oxy-2/deltavr/obsidian files/week1 thirdspace/monizjoao/Screenshot 2026-09-20 193455.png

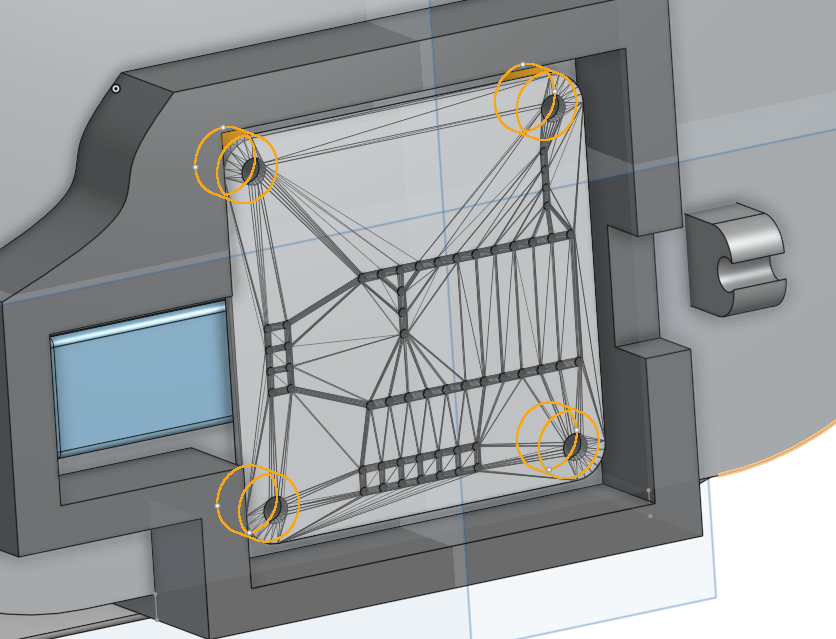
obsidian files/week1 thirdspace/monizjoao/Screenshot 2026-09-20 193455.png
