oxy-2/deltavr/obsidian files/week1 thirdspace/merekelene/emulation software showcase.png

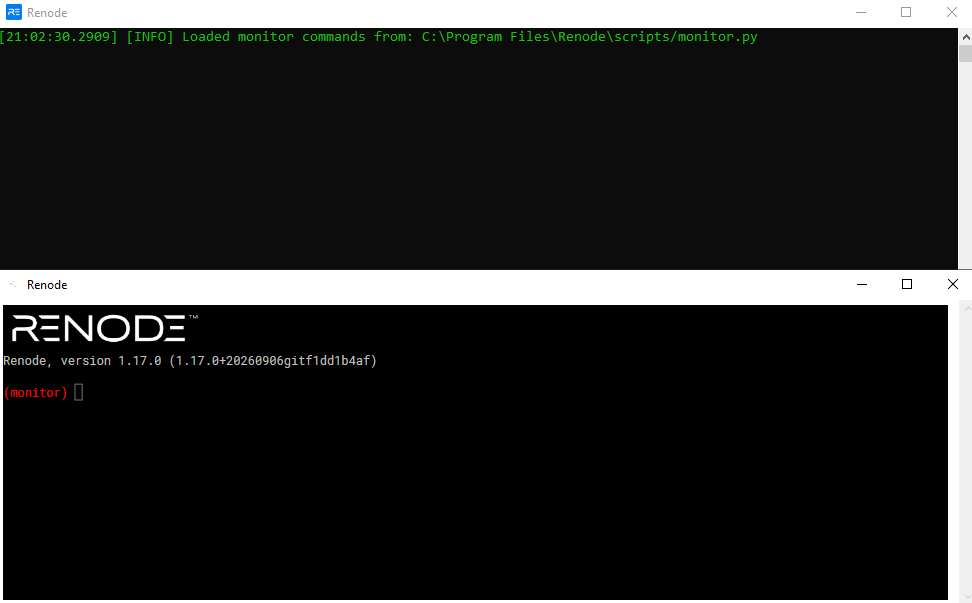
obsidian files/week1 thirdspace/merekelene/emulation software showcase.png
