oxy-2/deltavr/obsidian files/week1 thirdspace/merekelene/emulation software.png

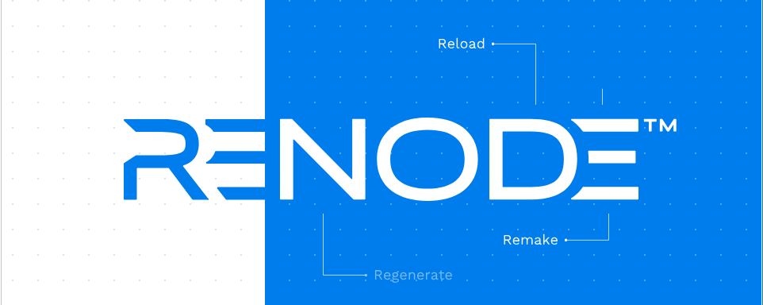
obsidian files/week1 thirdspace/merekelene/emulation software.png
