oxy-2/deltavr/obsidian files/week1 thirdspace/merekelene/pcb.png

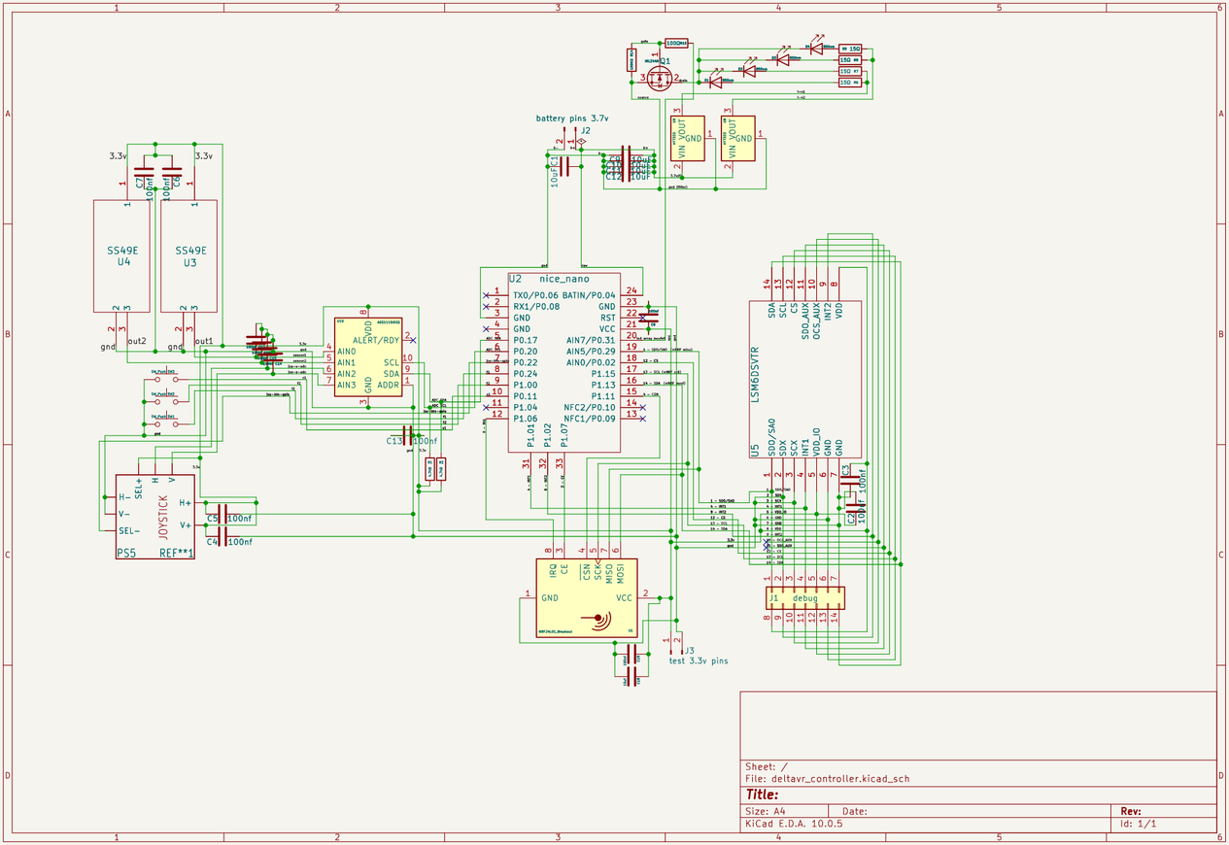
obsidian files/week1 thirdspace/merekelene/pcb.png
