oxy-2/deltavr/obsidian files/week1 thirdspace/merekelene/readable gpio pin conections.png

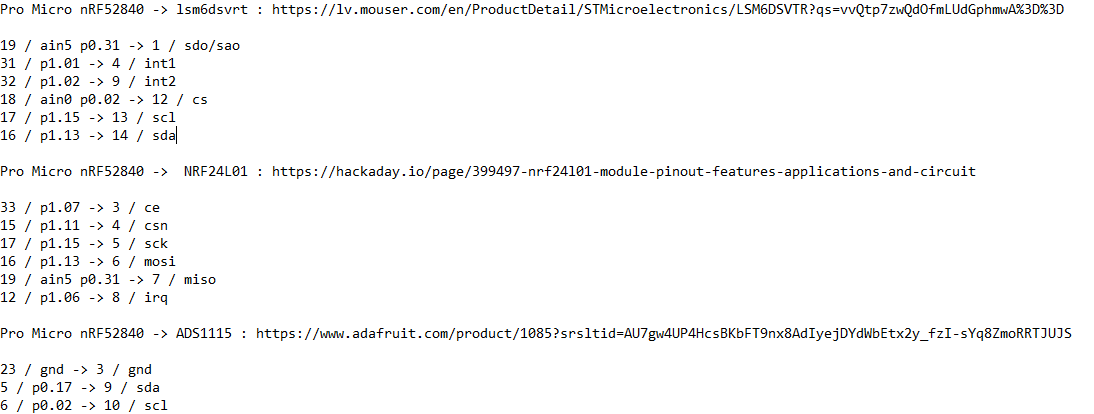
obsidian files/week1 thirdspace/merekelene/readable gpio pin conections.png
