oxy-2/deltavr/obsidian files/week1 thirdspace/monizjoao/Pasted image 20260920193406.png

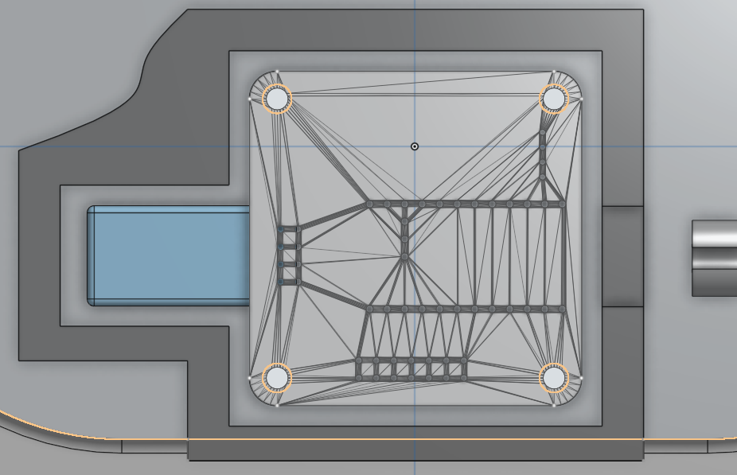
obsidian files/week1 thirdspace/monizjoao/Pasted image 20260920193406.png
