oxy-2/deltavr/obsidian files/week1 thirdspace/monizjoao/Pasted image 20260920201033.png

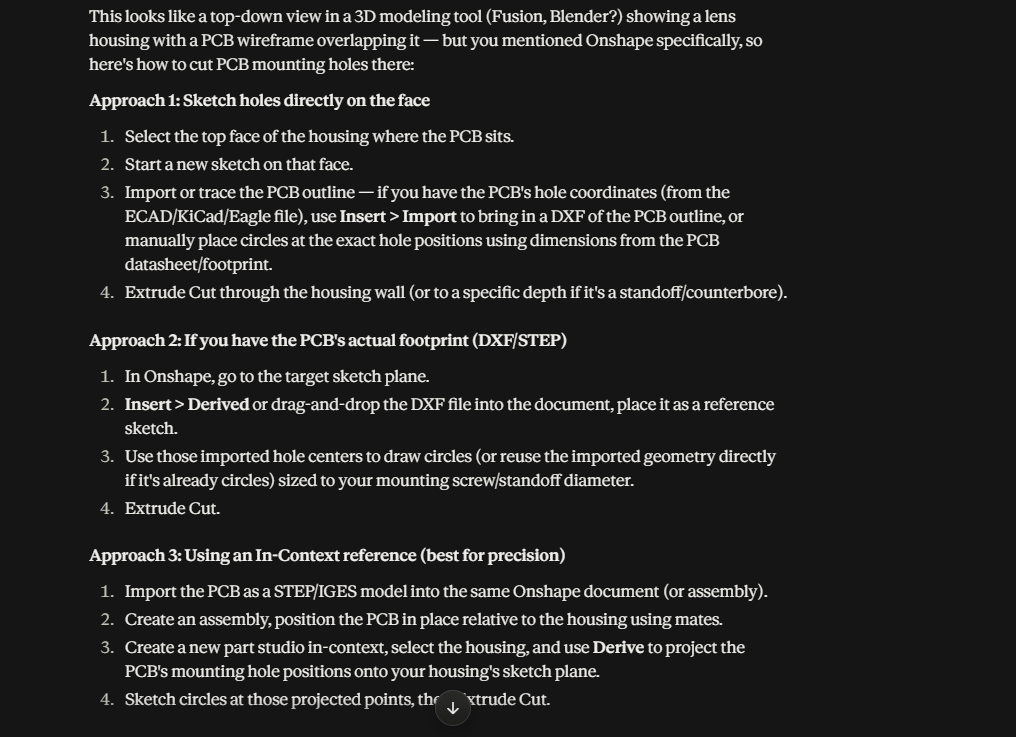
obsidian files/week1 thirdspace/monizjoao/Pasted image 20260920201033.png
