oxy-2/deltavr/obsidian files/week1 thirdspace/monizjoao/Pasted image 20260920225639.png

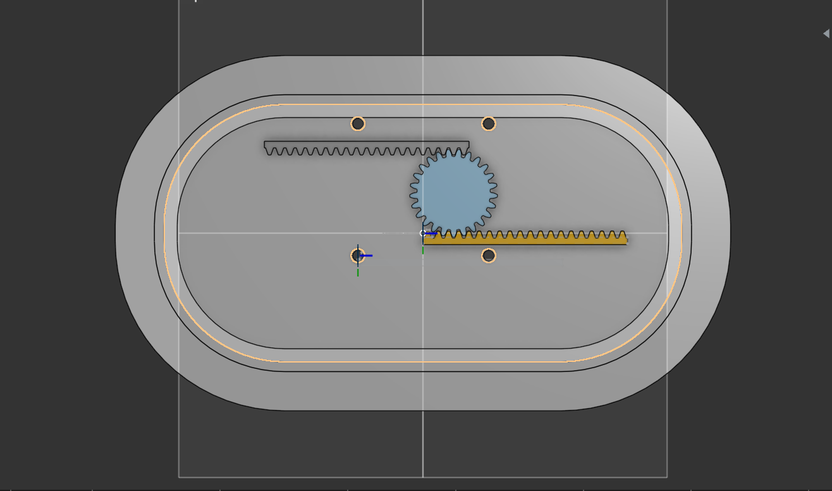
obsidian files/week1 thirdspace/monizjoao/Pasted image 20260920225639.png
