oxy-2/deltavr/obsidian files/week1 thirdspace/monizjoao/Pasted image 20260920233952.png

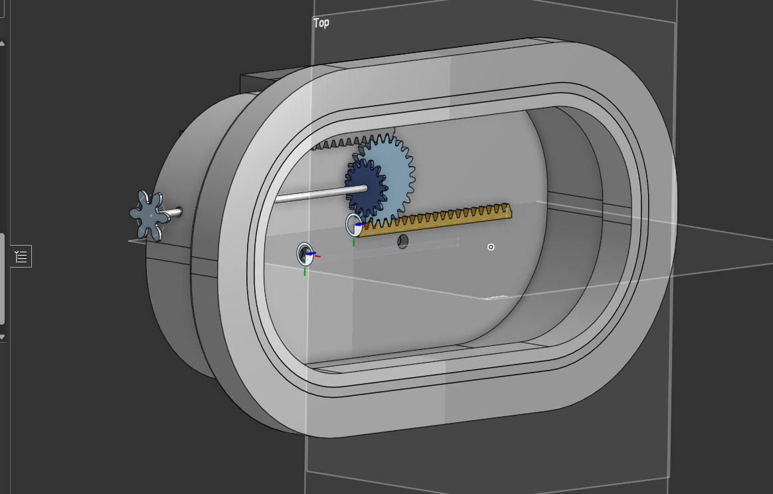
obsidian files/week1 thirdspace/monizjoao/Pasted image 20260920233952.png
