oxy-2/deltavr/obsidian files/week1 thirdspace/monizjoao/Pasted image 20260921000253.png

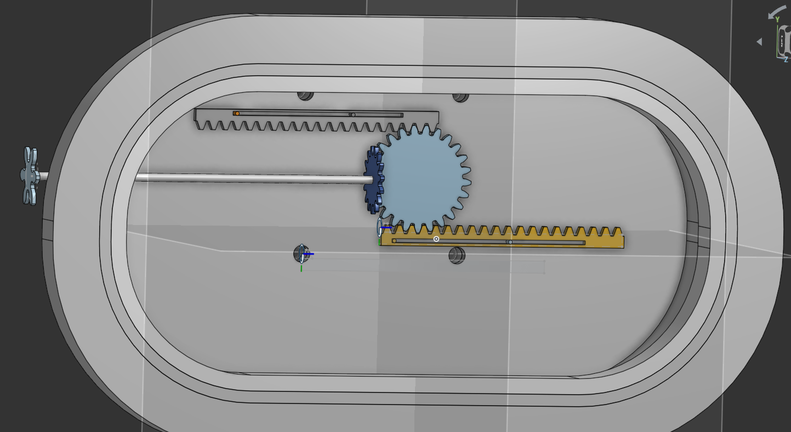
obsidian files/week1 thirdspace/monizjoao/Pasted image 20260921000253.png
