oxy-2/deltavr/obsidian files/week1 thirdspace/monizjoao/Pasted image 20260921001410.png

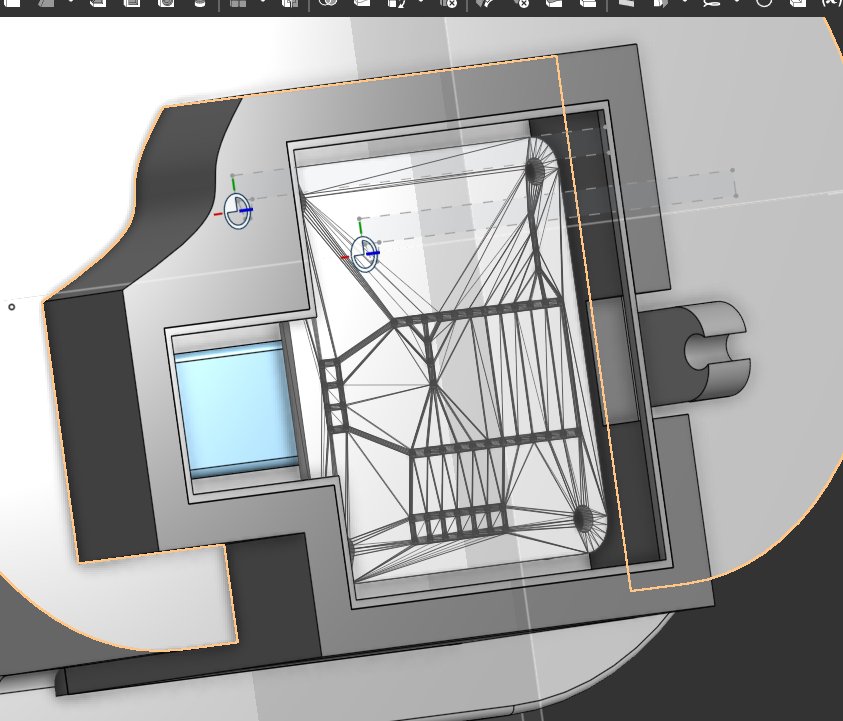
obsidian files/week1 thirdspace/monizjoao/Pasted image 20260921001410.png
