oxy-2/deltavr/obsidian files/week1 thirdspace/rhime7274/controller pcb.png

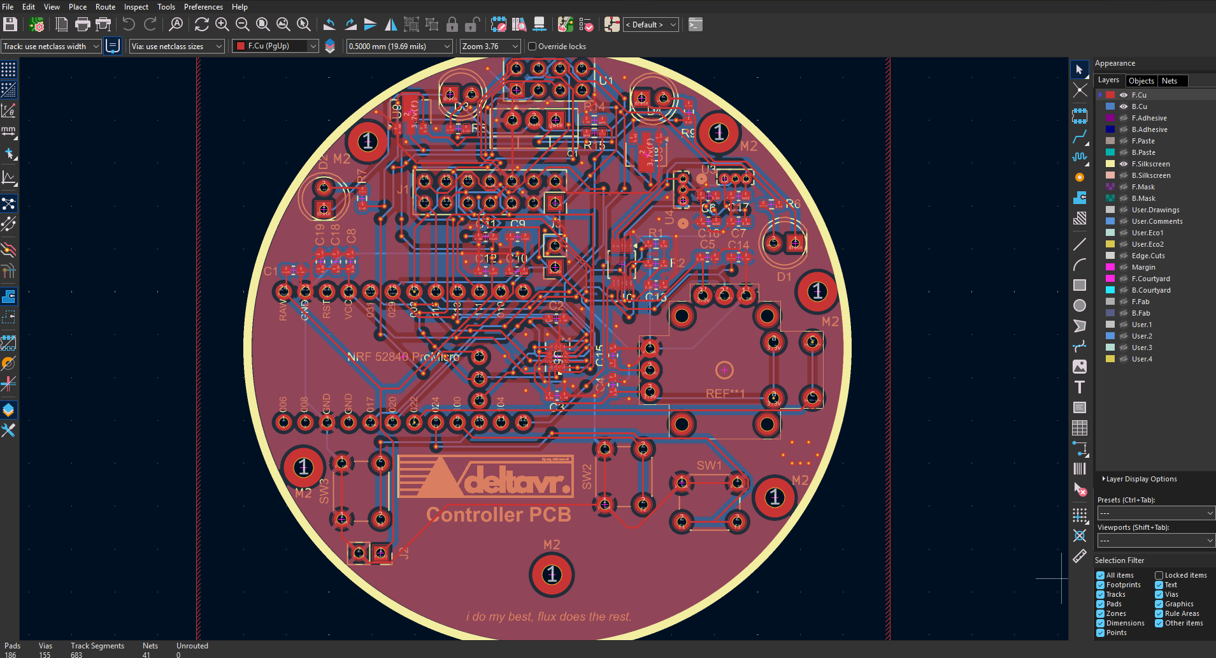
obsidian files/week1 thirdspace/rhime7274/controller pcb.png
