oxy-2/deltavr/obsidian files/week1 thirdspace/rhime7274/front page book.jpg

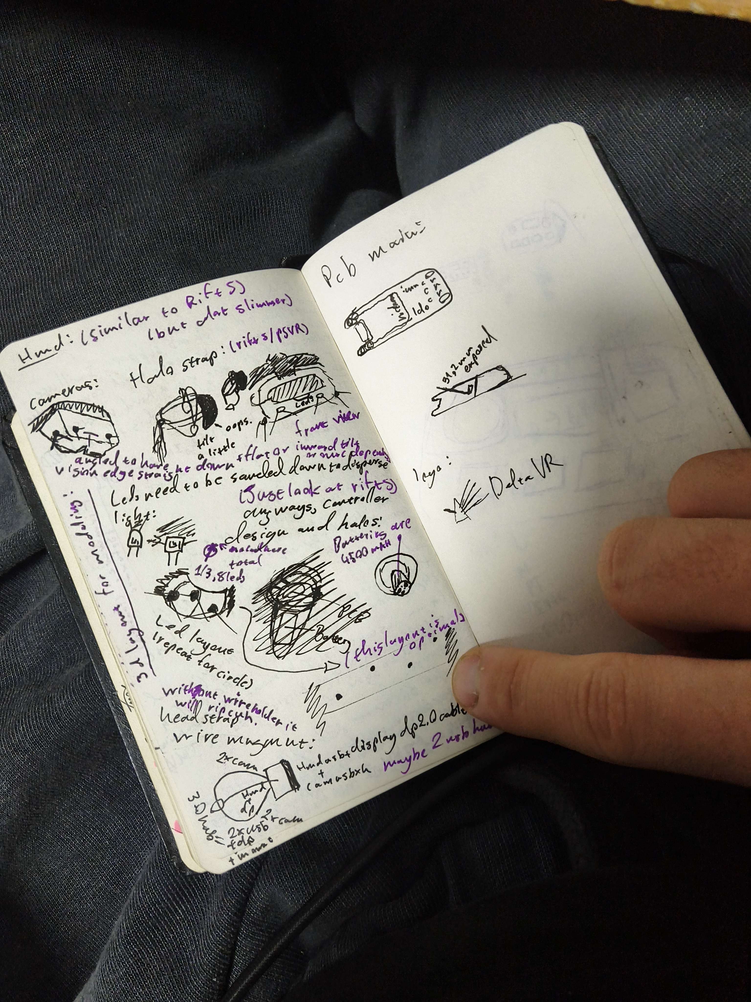
obsidian files/week1 thirdspace/rhime7274/front page book.jpg
