oxy-2/deltavr/obsidian files/week1 thirdspace/rhime7274/headset model.png

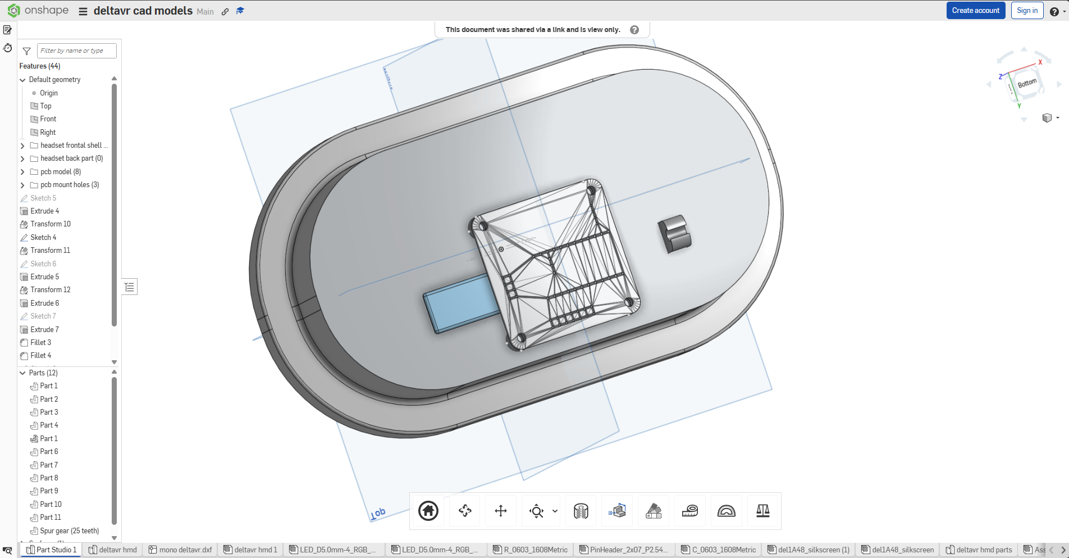
obsidian files/week1 thirdspace/rhime7274/headset model.png
