oxy-2/deltavr/obsidian files/week1 thirdspace/rhime7274/hmd pcb.jpg

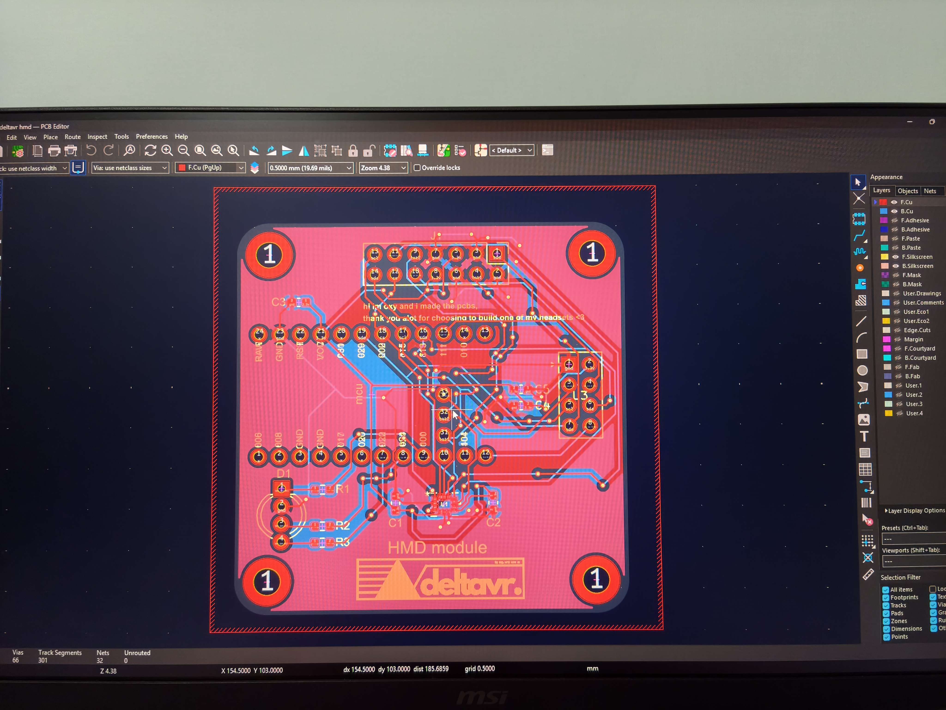
obsidian files/week1 thirdspace/rhime7274/hmd pcb.jpg
