oxy-2/deltavr/obsidian files/week2 thirdspace/merekelene/camera and lenses.png

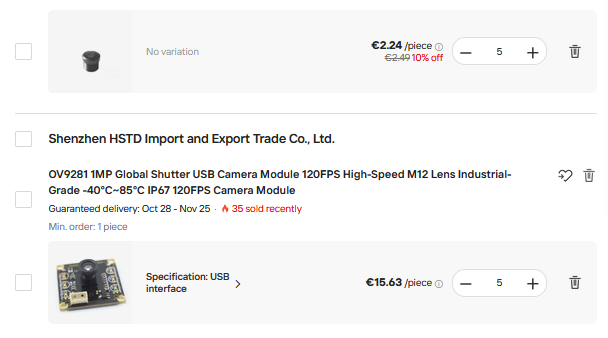
obsidian files/week2 thirdspace/merekelene/camera and lenses.png
