oxy-2/deltavr/obsidian files/week2 thirdspace/merekelene/file system showcase.png

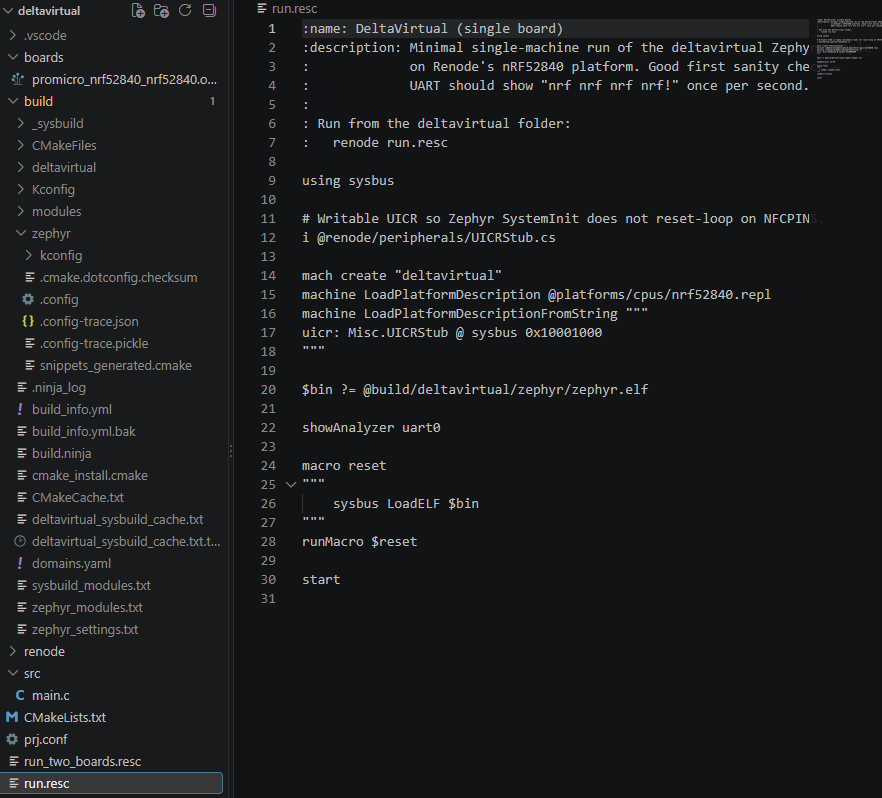
obsidian files/week2 thirdspace/merekelene/file system showcase.png
