oxy-2/deltavr/obsidian files/week2 thirdspace/merekelene/Gpio naming showcase.png

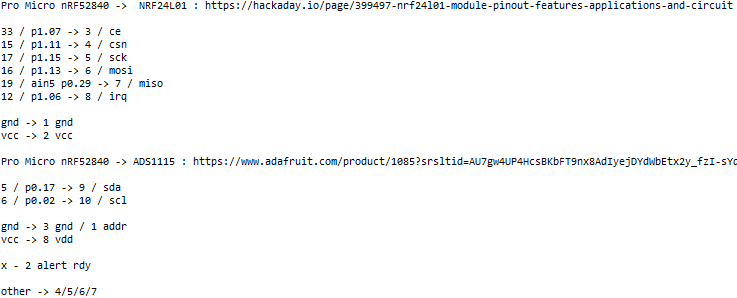
obsidian files/week2 thirdspace/merekelene/Gpio naming showcase.png
