oxy-2/deltavr/obsidian files/week2 thirdspace/merekelene/new radio module.png

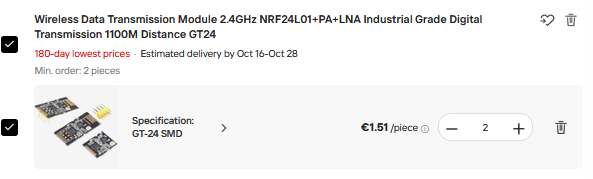
obsidian files/week2 thirdspace/merekelene/new radio module.png
