oxy-2/deltavr/obsidian files/week2 thirdspace/merekelene/uncompiled c code that will become an elf file.png

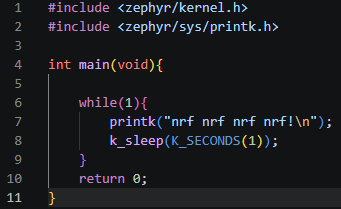
obsidian files/week2 thirdspace/merekelene/uncompiled c code that will become an elf file.png
