oxy-2/deltavr/obsidian files/week2 thirdspace/monizjoao/Pasted image 20260927151539.png

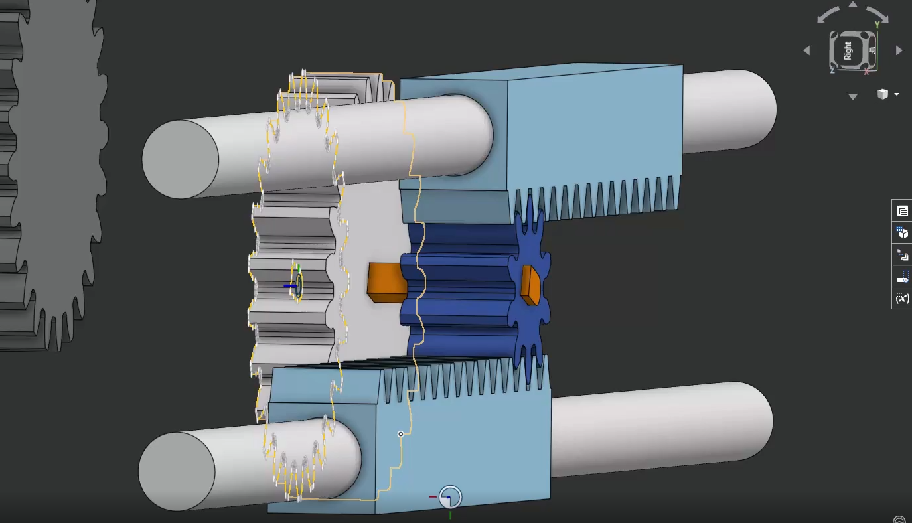
obsidian files/week2 thirdspace/monizjoao/Pasted image 20260927151539.png
