oxy-2/deltavr/obsidian files/week2 thirdspace/monizjoao/Pasted image 20260927153908.png

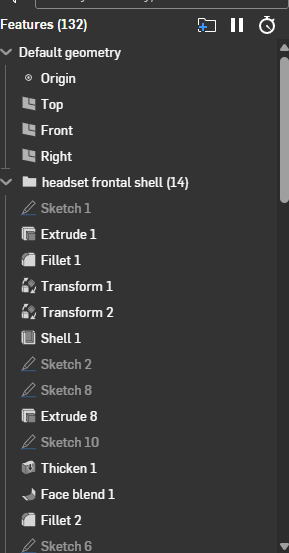
obsidian files/week2 thirdspace/monizjoao/Pasted image 20260927153908.png
