oxy-2/deltavr/obsidian files/week2 thirdspace/monizjoao/Pasted image 20260927155630.png

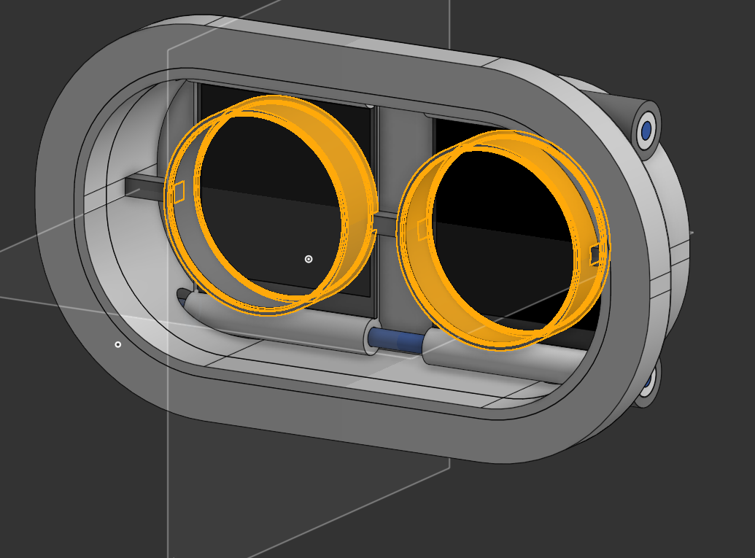
obsidian files/week2 thirdspace/monizjoao/Pasted image 20260927155630.png
