oxy-2/deltavr/obsidian files/week2 thirdspace/rhime7274/censored doc p2.png

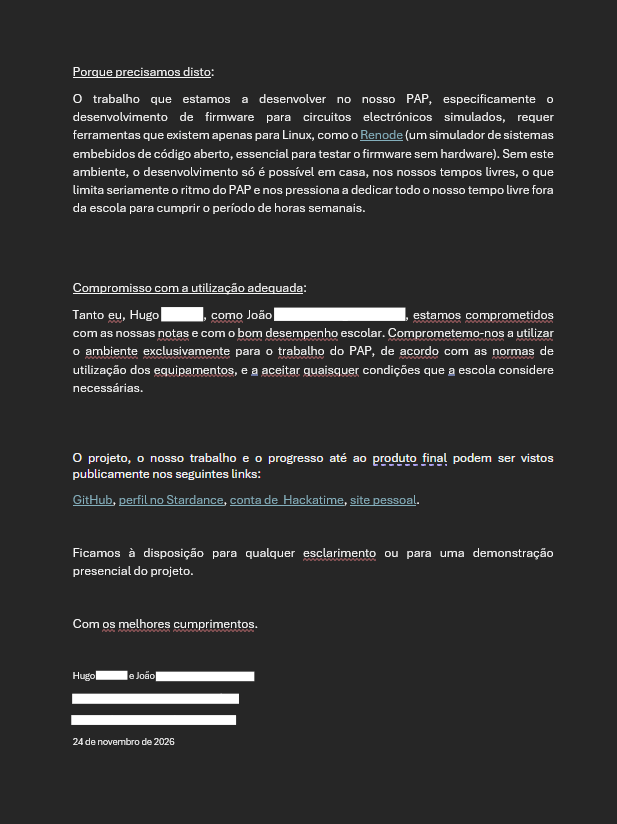
obsidian files/week2 thirdspace/rhime7274/censored doc p2.png
