oxy-2/deltavr/obsidian files/week2 thirdspace/rhime7274/dimensions.png

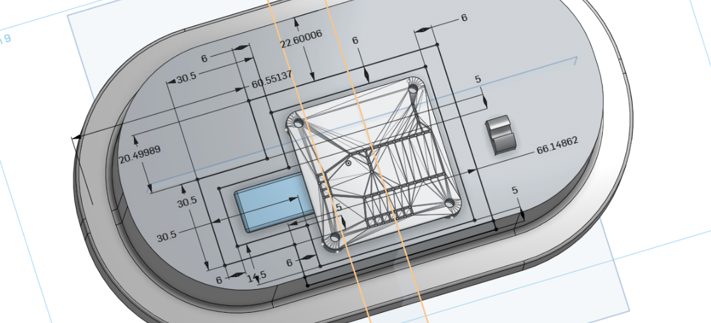
obsidian files/week2 thirdspace/rhime7274/dimensions.png
