oxy-2/deltavr/obsidian files/week2 thirdspace/rhime7274/front and pcb.png

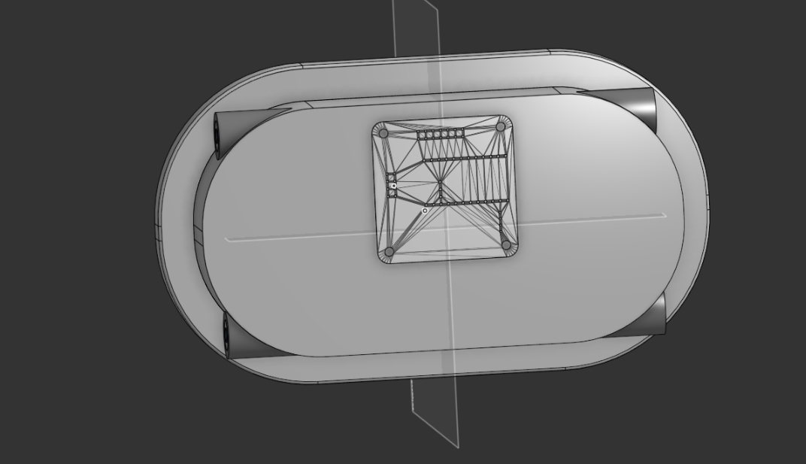
obsidian files/week2 thirdspace/rhime7274/front and pcb.png
