oxy-2/deltavr/obsidian files/week2 thirdspace/rhime7274/lenses and back.png

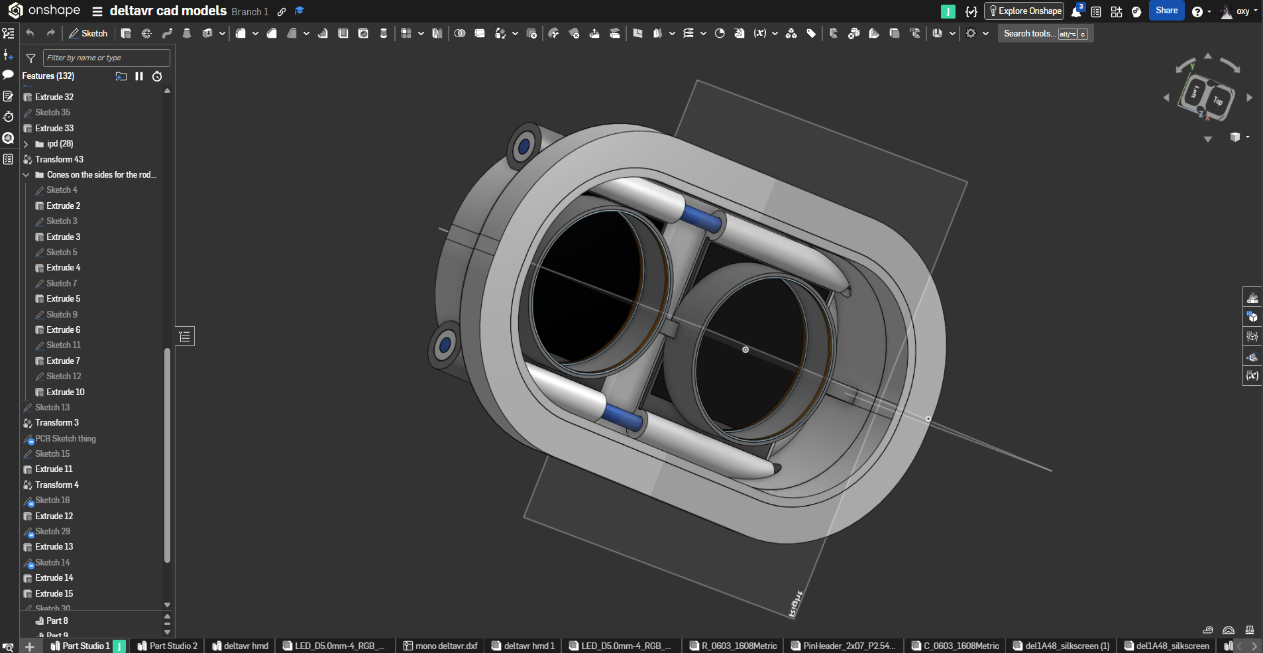
obsidian files/week2 thirdspace/rhime7274/lenses and back.png
