oxy-2/deltavr/obsidian files/week3 thirdspace/merekelene/launch file 2.png

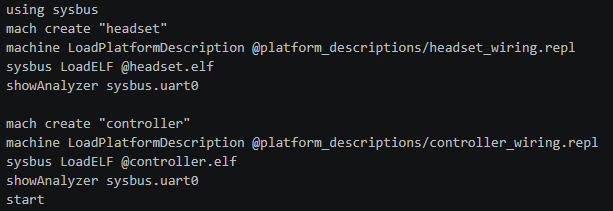
obsidian files/week3 thirdspace/merekelene/launch file 2.png
