oxy-2/deltavr/obsidian files/week3 thirdspace/merekelene/nrf board gpios.png

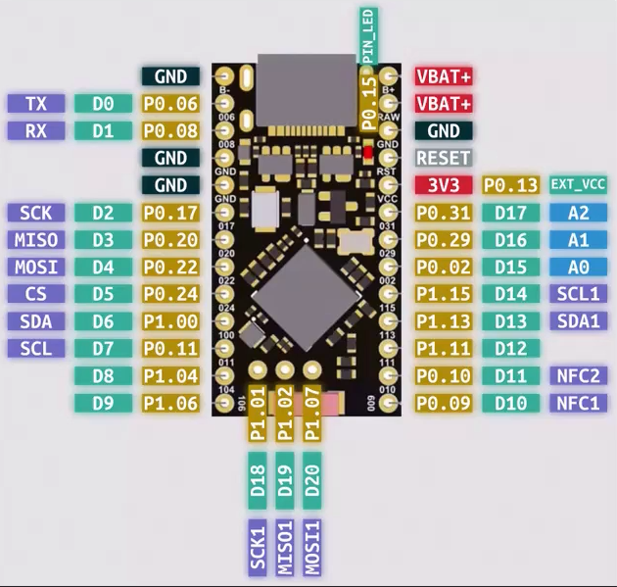
obsidian files/week3 thirdspace/merekelene/nrf board gpios.png
