oxy-2/deltavr/obsidian files/week3 thirdspace/monizjoao/image.png

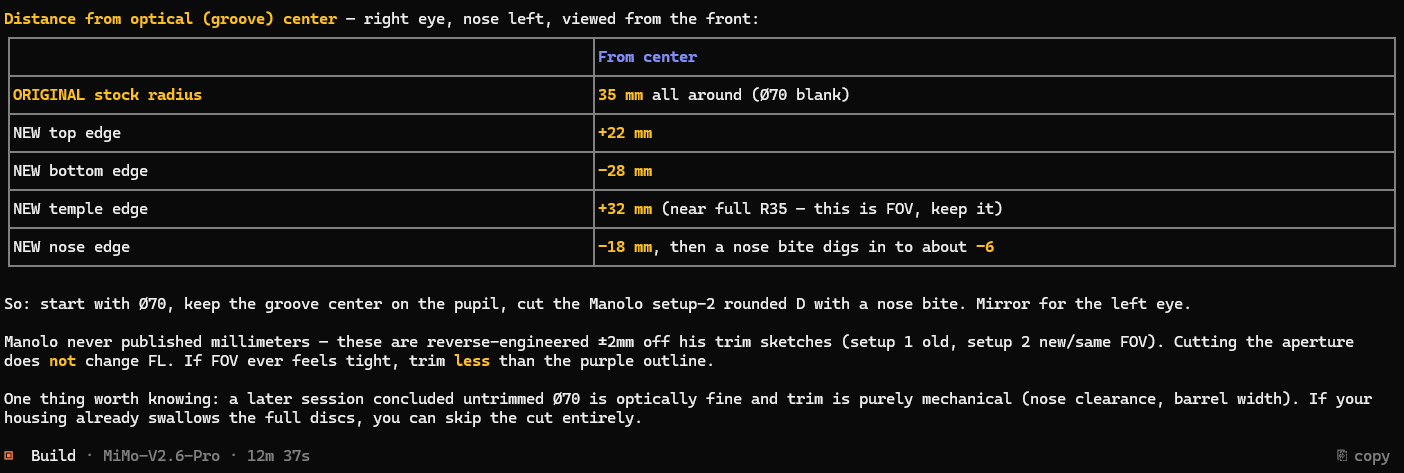
obsidian files/week3 thirdspace/monizjoao/image.png
