oxy-2/deltavr/obsidian files/week3 thirdspace/monizjoao/Pasted image 20261004205421.png

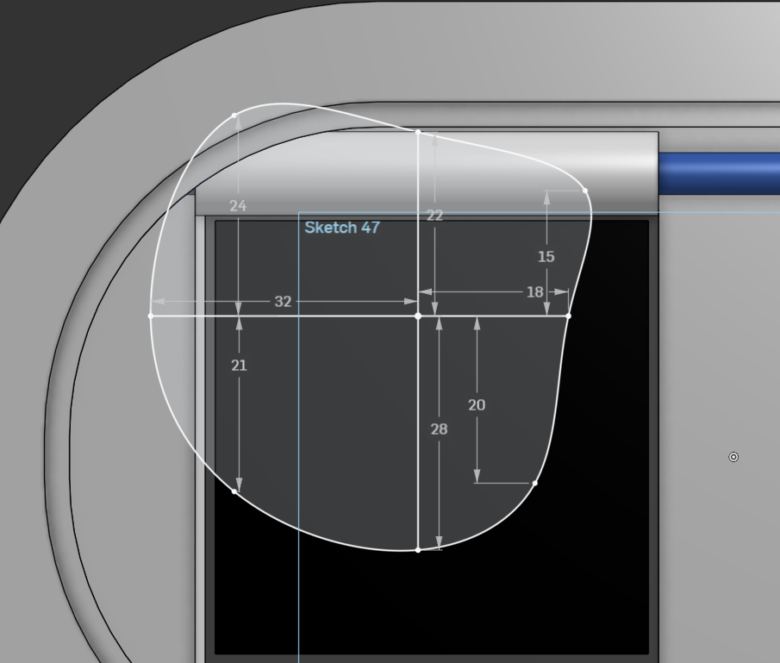
obsidian files/week3 thirdspace/monizjoao/Pasted image 20261004205421.png
