oxy-2/deltavr/obsidian files/week3 thirdspace/monizjoao/Pasted image 20261004220329.png

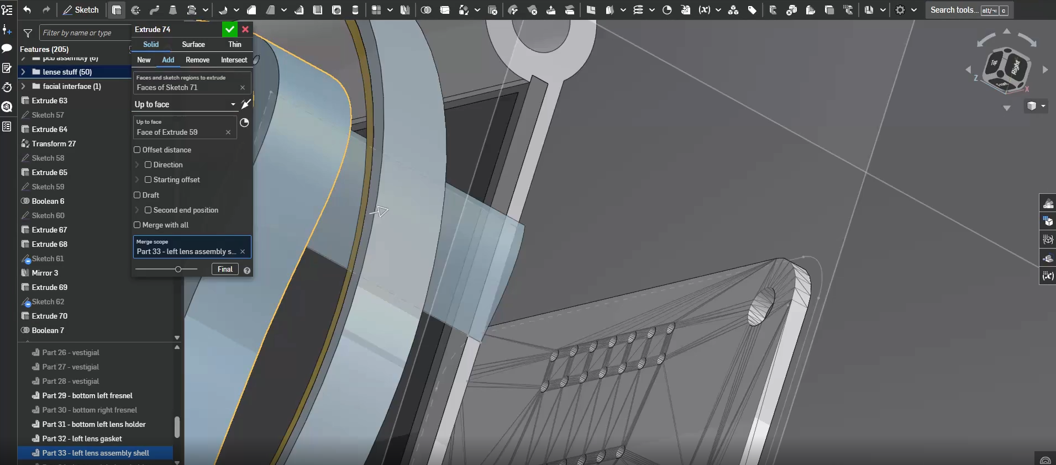
obsidian files/week3 thirdspace/monizjoao/Pasted image 20261004220329.png
