oxy-2/deltavr/obsidian files/week3 thirdspace/rhime7274/discord pins.png

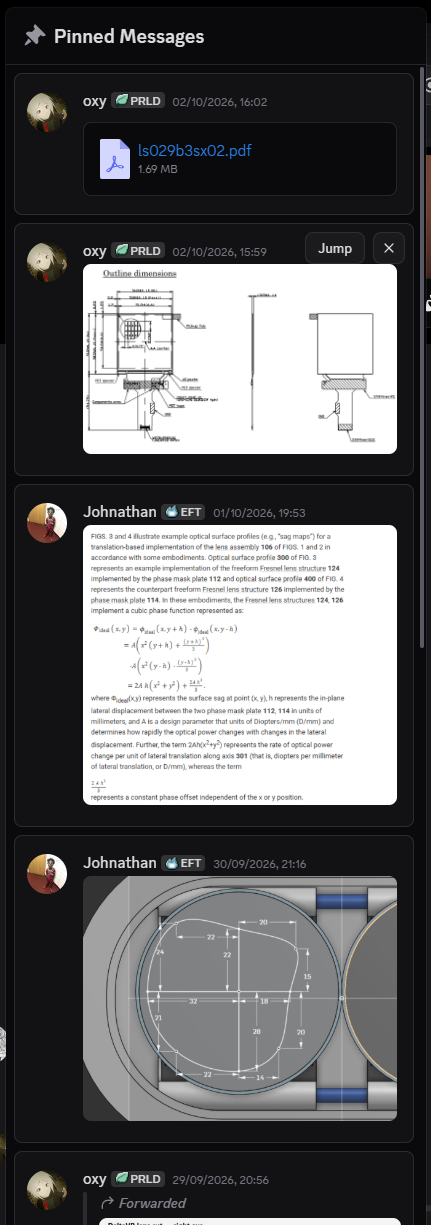
obsidian files/week3 thirdspace/rhime7274/discord pins.png
