oxy-2/deltavr/obsidian files/week3 thirdspace/rhime7274/feature list organization.png

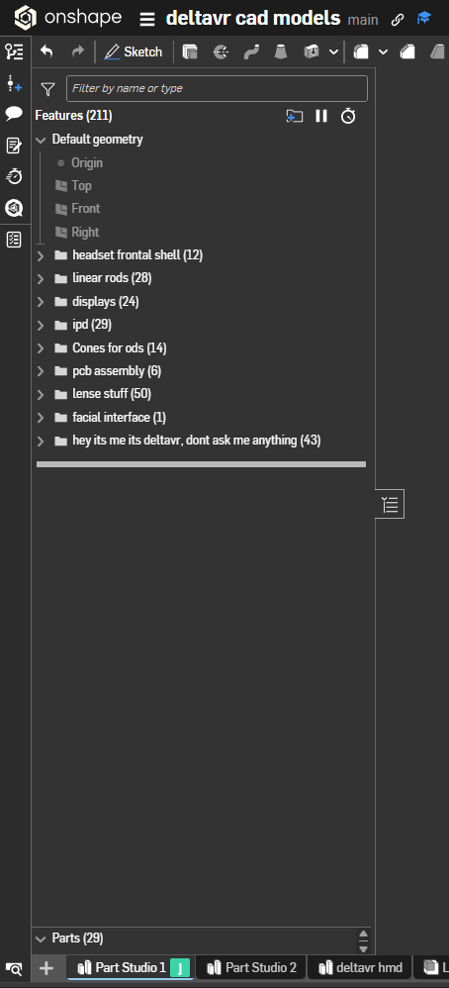
obsidian files/week3 thirdspace/rhime7274/feature list organization.png
