oxy-2/deltavr/obsidian files/week3 thirdspace/rhime7274/front pcb inset.png

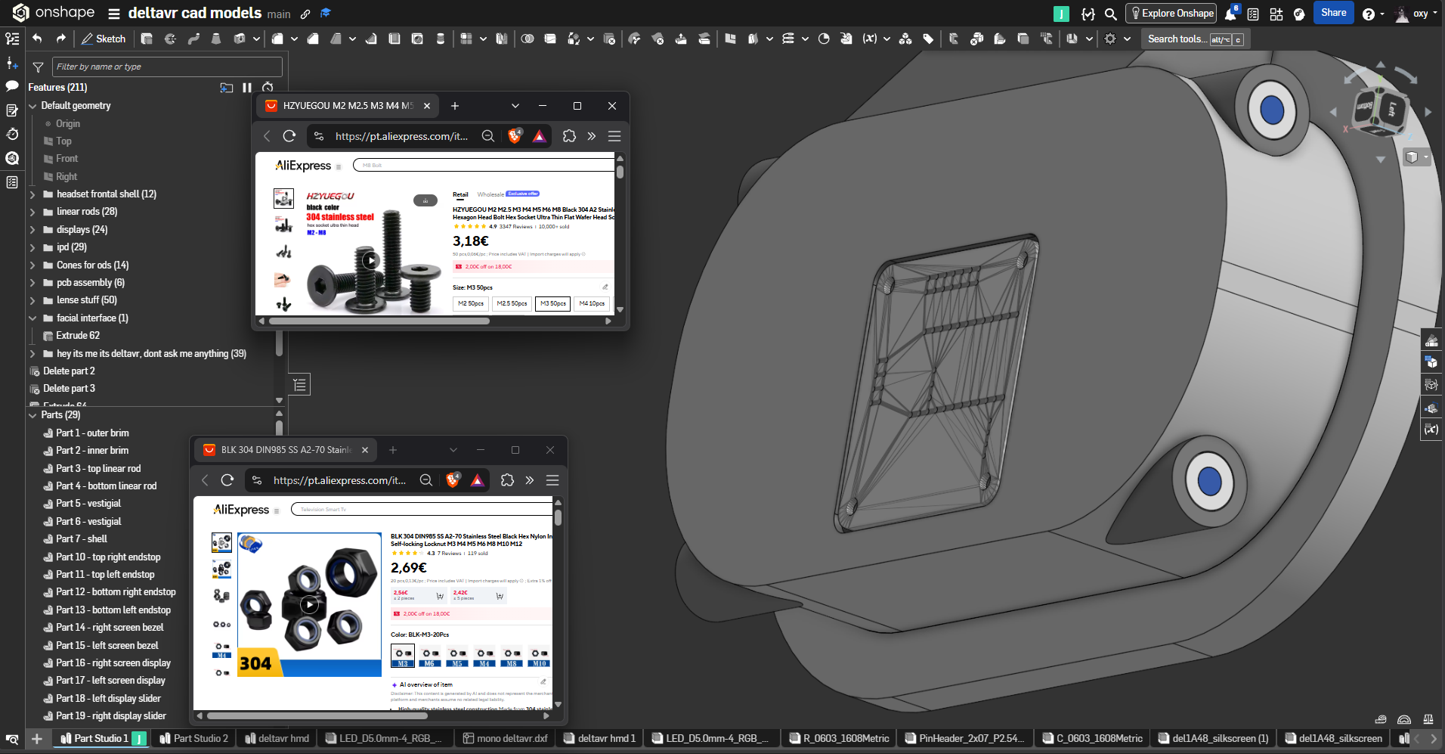
obsidian files/week3 thirdspace/rhime7274/front pcb inset.png
