oxy-2/deltavr/obsidian files/week3 thirdspace/rhime7274/mipi to hdmi board.png

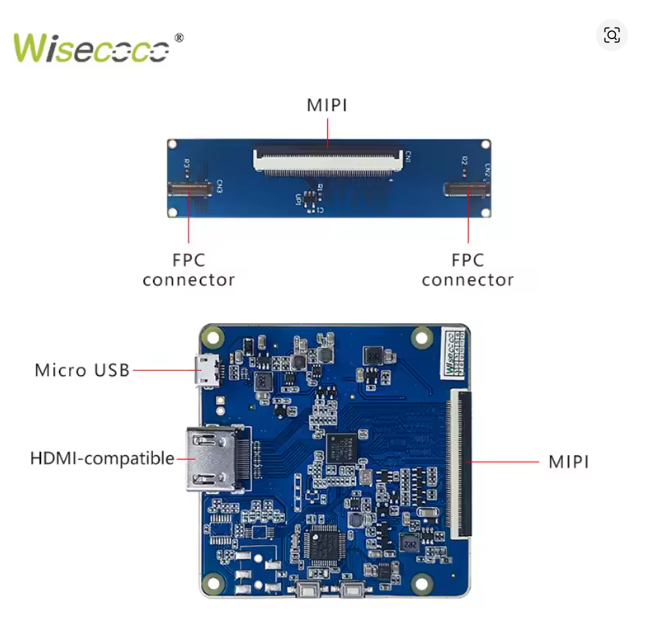
obsidian files/week3 thirdspace/rhime7274/mipi to hdmi board.png
