oxy-2/deltavr/obsidian files/week3 thirdspace/rhime7274/new lenses.png

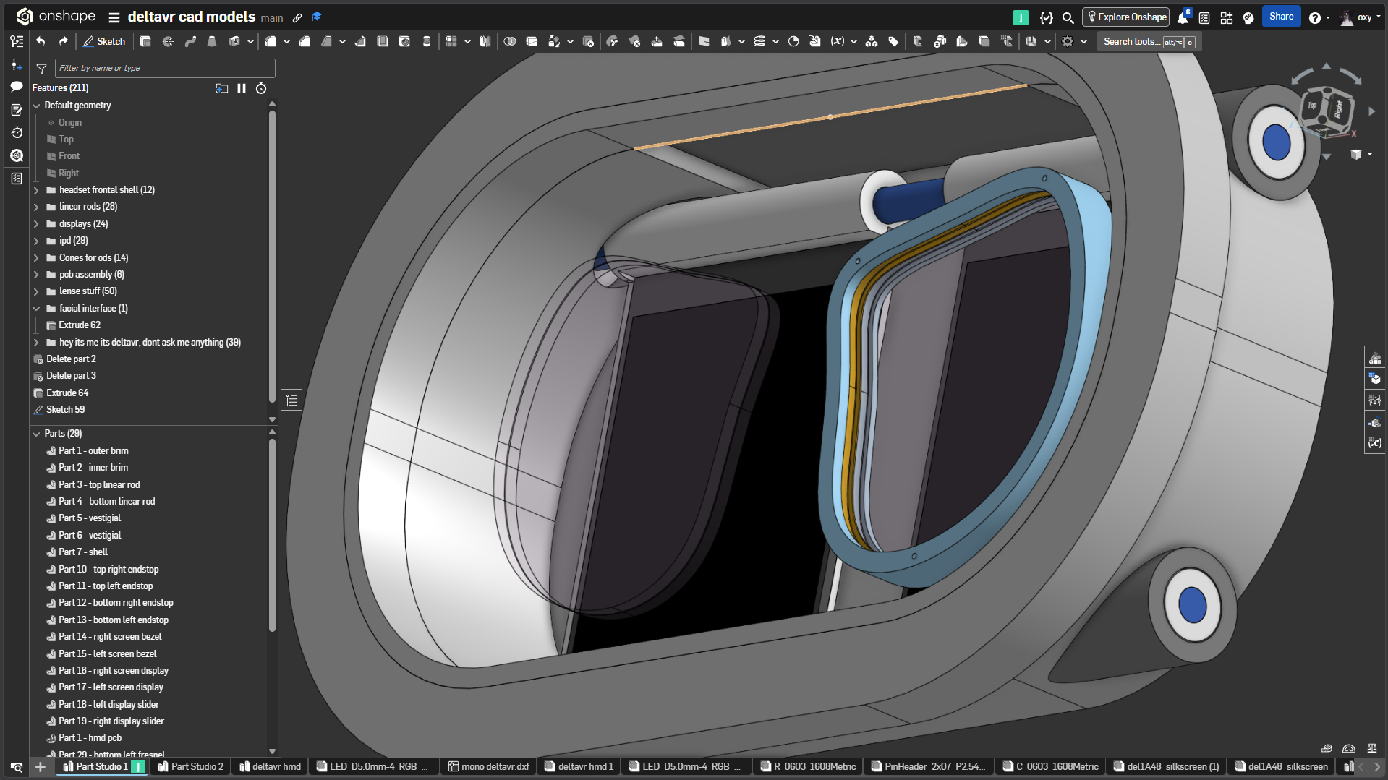
obsidian files/week3 thirdspace/rhime7274/new lenses.png
