oxy-2/deltavr/obsidian files/week3 thirdspace/rhime7274/the better mipi to hdmi board.png

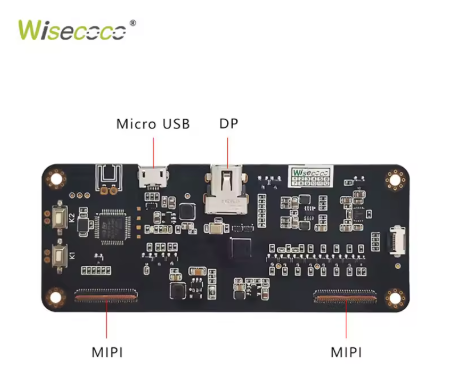
obsidian files/week3 thirdspace/rhime7274/the better mipi to hdmi board.png
