oxy-2/deltavr/obsidian files/week2 thirdspace/merekelene/cheeper components than on aliexpress.png

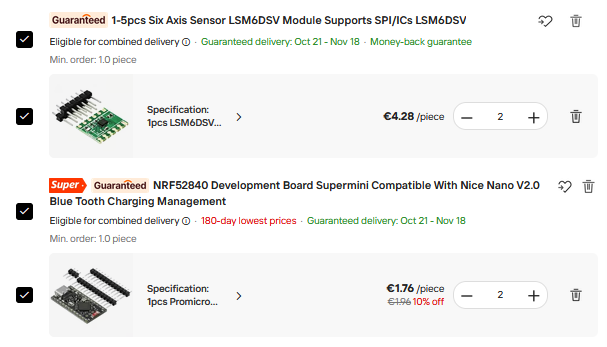
obsidian files/week2 thirdspace/merekelene/cheeper components than on aliexpress.png
