oxy-2/deltavr/obsidian files/week3 thirdspace/rhime7274/parts list organization.png

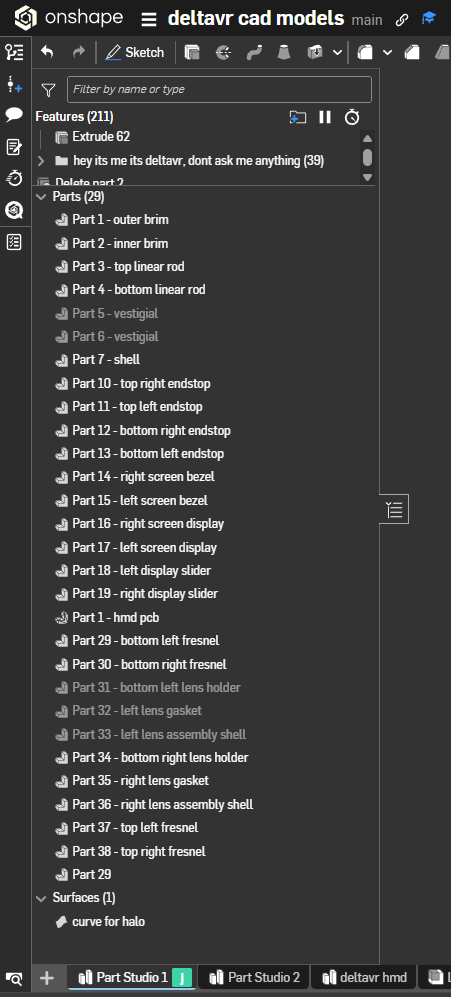
obsidian files/week3 thirdspace/rhime7274/parts list organization.png
