oxy-2/deltavr/obsidian files/week1 thirdspace/merekelene/laptop setup downloading.png

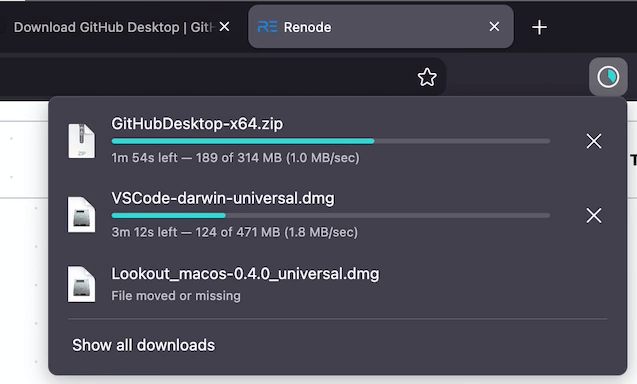
obsidian files/week1 thirdspace/merekelene/laptop setup downloading.png
