oxy-2/deltavr/obsidian files/week3 thirdspace/merekelene/install manual.png

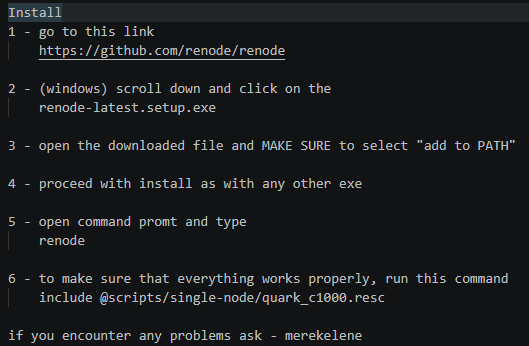
obsidian files/week3 thirdspace/merekelene/install manual.png
