oxy-2/deltavr/obsidian files/week3 thirdspace/merekelene/run manual.png

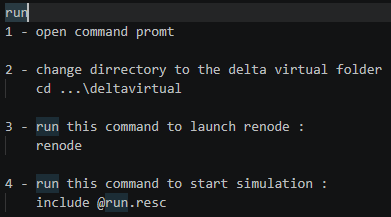
obsidian files/week3 thirdspace/merekelene/run manual.png
