oxy-2/deltavr/obsidian files/week1 thirdspace/merekelene/emulation software test run.png

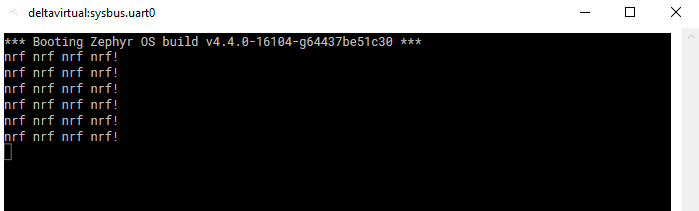
obsidian files/week1 thirdspace/merekelene/emulation software test run.png
